dirkandterra/NanoDashboard/ArduinoPastPrograms/GandL/GandL.h

#ifndef GandL_h
#define GandL_h

	int sendInfo(uint8_t gauge, uint16_t value);
  int sendVFD(uint8_t *c, uint8_t n);
	int testVFD(uint16_t value);
  extern void vfdPrep(void);
  void updateGuages_Lights(void);

#endif
